SaadTiwana/axelera/stm32G474 _firmware/pid.hpp

// Source: https://github.com/simplefoc/Arduino-FOC/blob/master/src/common/pid.cpp


#ifndef PID_HPP
#define PID_HPP

#include "time_utils.hpp"

/**
 *  PID controller class
 */
class PIDController {
public:
  /**
     *  
     * @param P - Proportional gain 
     * @param I - Integral gain
     * @param D - Derivative gain 
     * @param ramp - Maximum speed of change of the output value
     * @param limit - Maximum output value
     */
  PIDController(float P, float I, float D, float ramp, float limit);
  ~PIDController() = default;

  float operator()(float error);
  void reset();

  float P;            //!< Proportional gain
  float I;            //!< Integral gain
  float D;            //!< Derivative gain
  float output_ramp;  //!< Maximum speed of change of the output value
  float limit;        //!< Maximum output value

protected:
  float error_prev;              //!< last tracking error value
  float output_prev;             //!< last pid output value
  float integral_prev;           //!< last integral component value
  unsigned long timestamp_prev;  //!< Last execution timestamp
};


#endif  // PID_HPP
