SaadTiwana/axelera/stm32G474 _firmware/lowpass_filter.cpp

// From: https://github.com/simplefoc/Arduino-FOC/blob/master/src/common/lowpass_filter.cpp

#include "lowpass_filter.hpp"

LowPassFilter::LowPassFilter(float time_constant)
    : Tf(time_constant)
    , y_prev(0.0f)
{
    timestamp_prev = _micros();
}


float LowPassFilter::operator() (float x)
{
    unsigned long timestamp = _micros();
    float dt = (timestamp - timestamp_prev)*1e-6f;

    if (dt < 0.0f ) dt = 1e-3f;
    else if(dt > 0.3f) {
        y_prev = x;
        timestamp_prev = timestamp;
        return x;
    }

    float alpha = Tf/(Tf + dt);
    float y = alpha*y_prev + (1.0f - alpha)*x;
    y_prev = y;
    timestamp_prev = timestamp;
    return y;
}
