SaadTiwana/axelera/stm32G474 _firmware/time_utils.hpp

// Source: https://github.com/simplefoc/Arduino-FOC/blob/master/src/common/time_utils.h


#ifndef TIME_UTILS_H
#define TIME_UTILS_H

#include "foc_utils.hpp"

/** 
 * Function implementing delay() function in milliseconds 
 * - blocking function
 * - hardware specific

 * @param ms number of milliseconds to wait
 */
void _delay(unsigned long ms);

/** 
 * Function implementing timestamp getting function in microseconds
 * hardware specific
 */
unsigned long _micros();


#endif
